jbilander/A500_RGBtoHDMI/images/A500_RGBtoHDMI_pic3.png

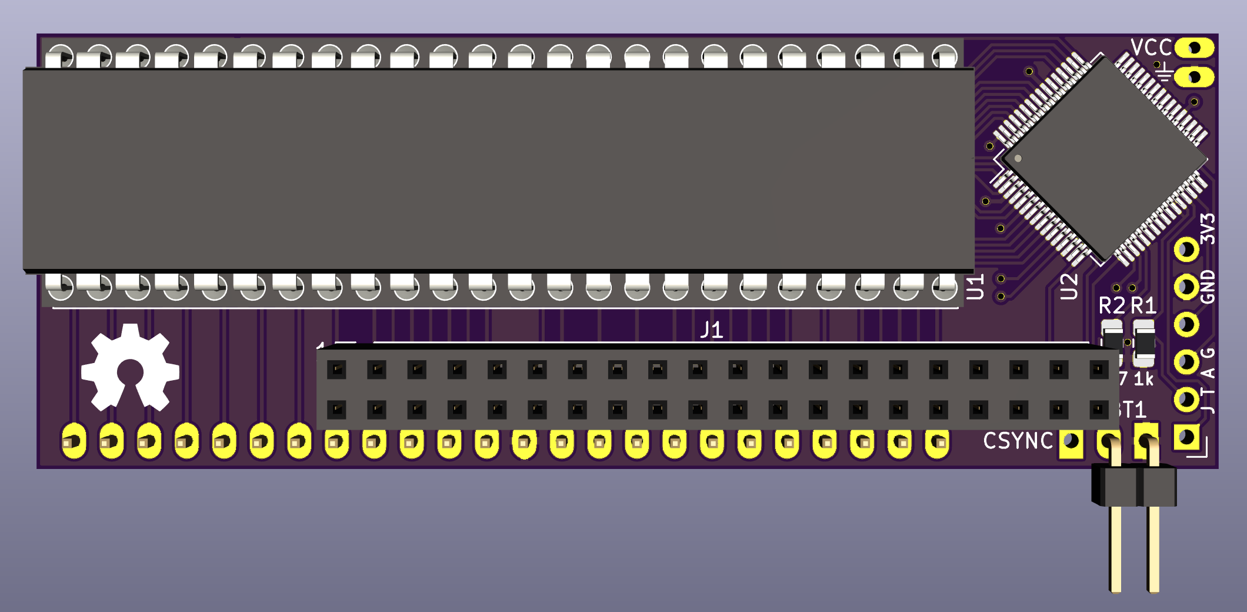
images/A500_RGBtoHDMI_pic3.png
