jbilander/A500_RGBtoHDMI/images/A500_RGBtoHDMI_pic16.jpg

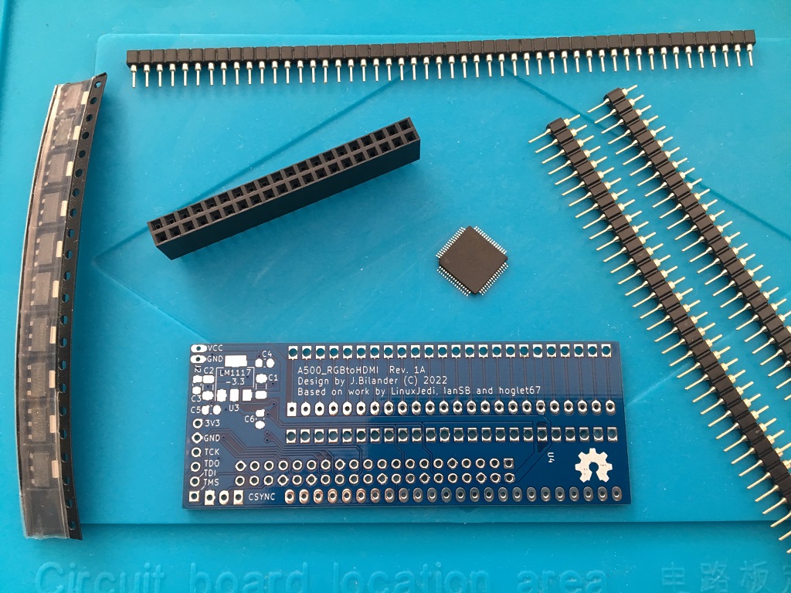
images/A500_RGBtoHDMI_pic16.jpg
